chaurais/STM32_MIDI_CTK240/Docs/20211125_080620.jpg

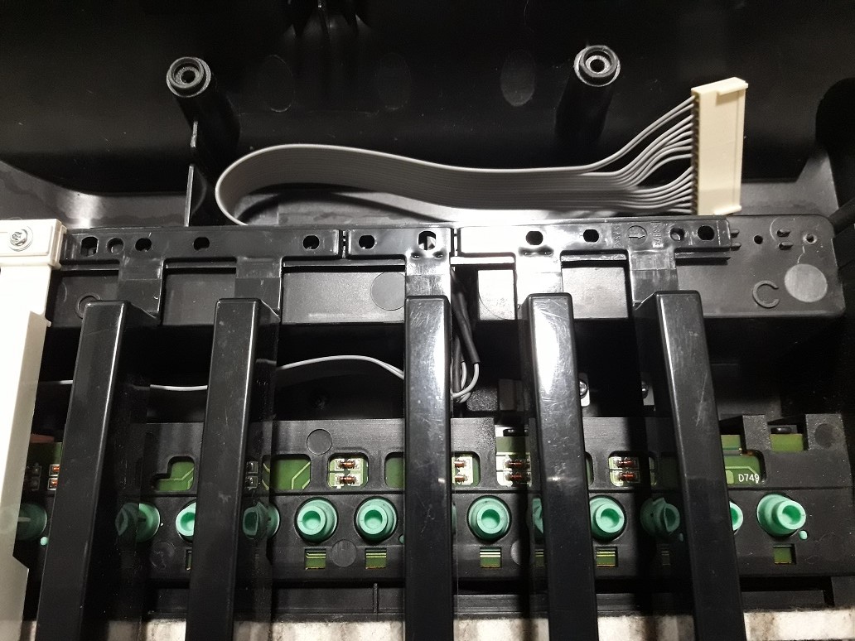
Docs/20211125_080620.jpg
