chaurais/STM32_MIDI_CTK240/Docs/20211125_182307.jpg

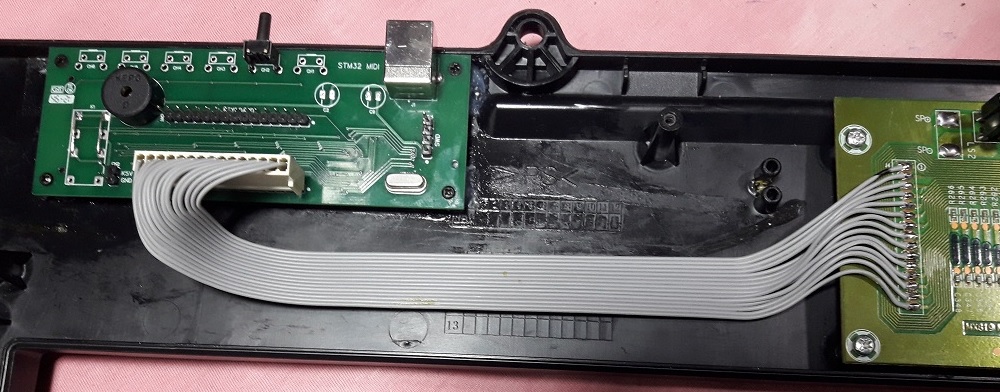
Docs/20211125_182307.jpg
