chaurais/STM32_MIDI_CTK240/Docs/20220116_143829.jpg

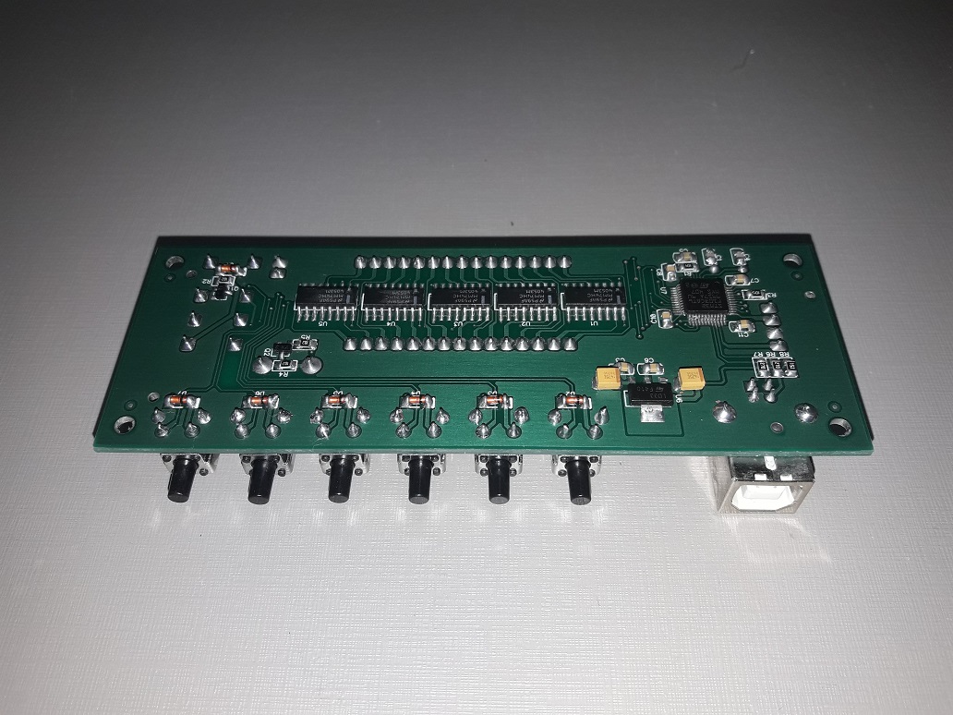
Docs/20220116_143829.jpg
