chaurais/STM32_MIDI_CTK240/Docs/20220116_143929.jpg

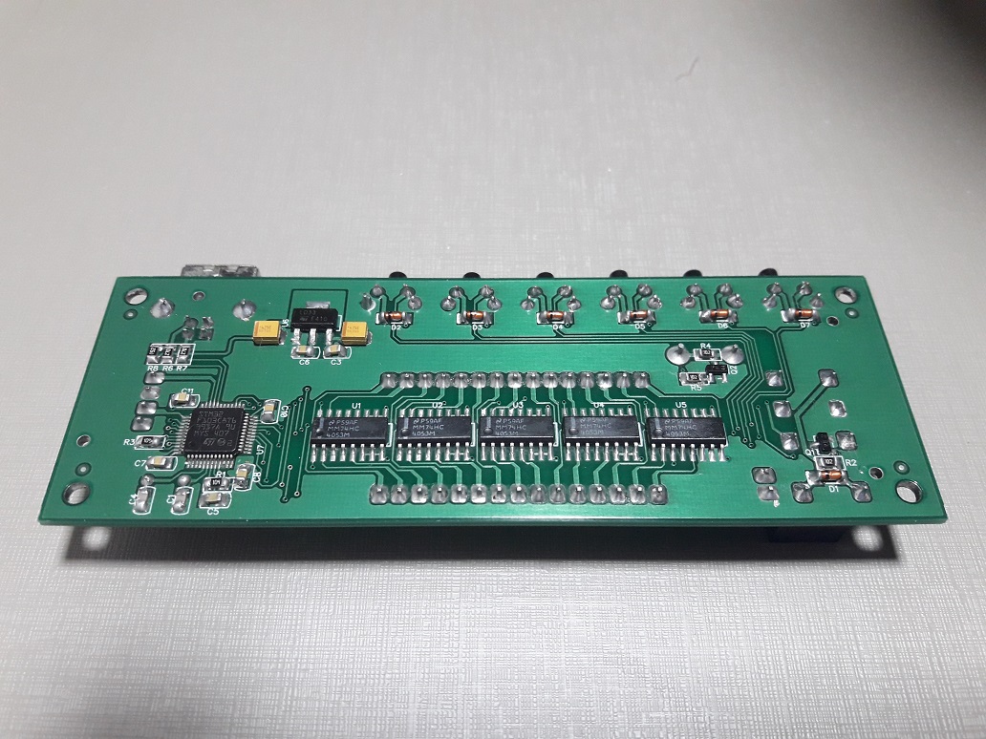
Docs/20220116_143929.jpg
