chaurais/STM32_MIDI_CTK240/Docs/20220116_144431.jpg

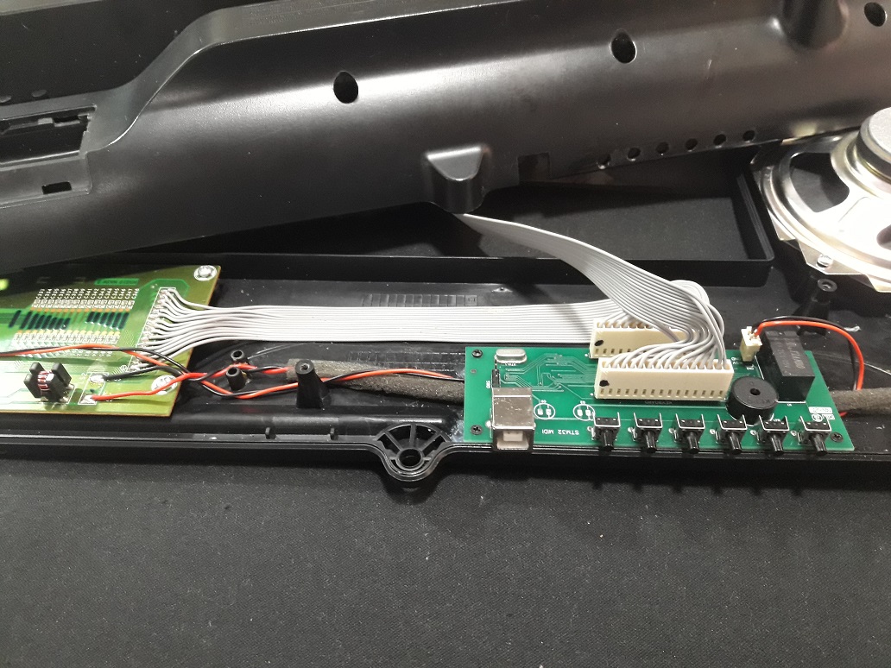
Docs/20220116_144431.jpg
