chaurais/STM32_MIDI_CTK240/Docs/20220116_144501.jpg

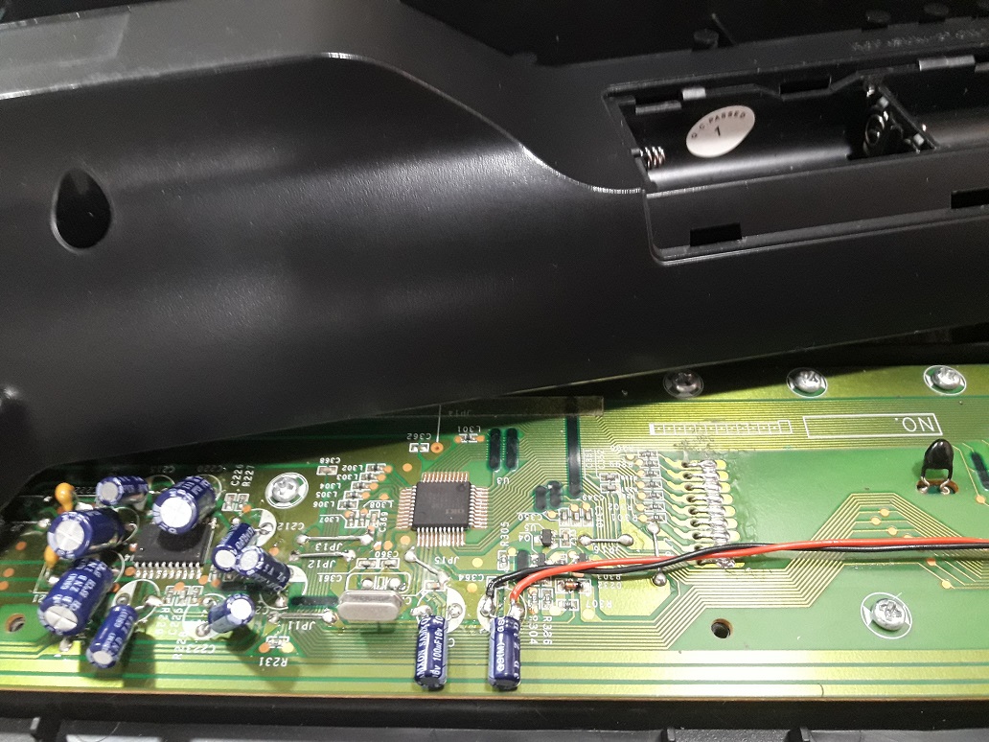
Docs/20220116_144501.jpg
