chaurais/STM32_MIDI_CTK240/Docs/20220116_173726.jpg

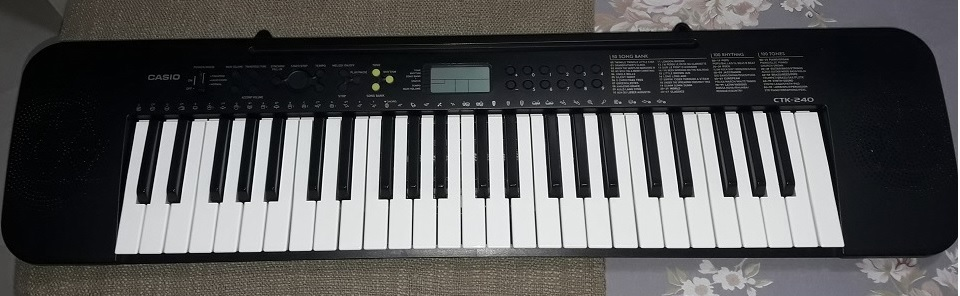
Docs/20220116_173726.jpg
